harbaum/galagino/images/menu.png

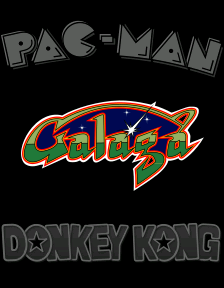
images/menu.png
