harbaum/galagino/galagino/1942_logo.h

const unsigned short _1942_logo[] = {
1,
1, 5841, 0, 41488, 1, 16, 33296, 16648, 1, 29, 0, 1, 21, 33296, 49944, 1, 
4, 1057, 8192, 1, 32, 0, 1, 4, 33296, 8192, 1, 39, 0, 16648, 1, 35, 
33296, 16648, 1, 27, 0, 19555, 57079, 1, 16, 65535, 37524, 1, 27, 0, 16648, 54965, 
1, 27, 65535, 30125, 1, 31, 0, 60250, 1, 26, 65535, 30125, 1, 17, 0, 5021, 
1, 35, 65535, 40431, 59193, 1, 25, 0, 36203, 1, 1, 57079, 1, 14, 23783, 40431, 
65535, 45716, 1, 26, 0, 24840, 63421, 65535, 48887, 1, 20, 23783, 64478, 1, 3, 56022, 
40431, 65535, 45716, 1, 29, 0, 33296, 15591, 65535, 32239, 1, 2, 23783, 32239, 1, 20, 
65535, 30125, 1, 17, 0, 5021, 65535, 40431, 1, 32, 23783, 32239, 65535, 32239, 42545, 1, 
23, 0, 44659, 65535, 57079, 19819, 1, 14, 0, 19555, 65535, 37524, 1, 25, 0, 24840, 
6342, 65535, 64478, 9249, 1, 25, 0, 42545, 40431, 65535, 52851, 1, 28, 0, 53908, 65535, 
63421, 1, 23, 0, 26954, 65535, 30125, 1, 17, 0, 5021, 65535, 52058, 1, 33, 0, 
5021, 65535, 32239, 34353, 1, 21, 0, 61307, 65535, 57079, 60250, 1, 15, 0, 19555, 65535, 
45716, 1, 24, 0, 24840, 14534, 65535, 64478, 1057, 1, 27, 0, 18762, 1, 1, 57079, 
60250, 1, 26, 0, 42545, 57079, 48887, 17441, 1, 23, 0, 26954, 65535, 30125, 1, 17, 
0, 5021, 65535, 52058, 1, 34, 0, 13477, 65535, 15591, 17441, 1, 19, 0, 20876, 65535, 
57079, 52058, 1, 16, 0, 11363, 65535, 45716, 1, 23, 0, 33296, 22726, 65535, 64478, 1057, 
1, 29, 0, 11363, 65535, 48887, 10306, 1, 25, 0, 31182, 65535, 61307, 1, 24, 0, 
35146, 65535, 30125, 1, 17, 0, 5021, 65535, 52058, 1, 34, 0, 8192, 38317, 65535, 7135, 
1057, 1, 17, 0, 29068, 65535, 48887, 35146, 1, 17, 0, 11363, 65535, 45716, 1, 22, 
0, 41488, 31182, 65535, 47830, 49944, 1, 31, 0, 4228, 65535, 40431, 42545, 1, 23, 0, 
36467, 65535, 56022, 8192, 1, 24, 0, 35146, 65535, 21933, 1, 17, 0, 5021, 65535, 52058, 
1, 35, 0, 16648, 63421, 65535, 64478, 58136, 1, 14, 0, 49424, 54445, 65535, 57079, 44429, 
1, 6, 51044, 1, 5, 42852, 41224, 1, 4, 0, 11363, 65535, 45716, 1, 21, 0, 
1074, 64214, 65535, 23519, 2421, 1, 5, 42852, 1, 7, 51044, 1, 8, 59244, 25923, 1, 
9, 0, 62364, 65535, 15591, 9249, 1, 18, 0, 24584, 1, 1, 17202, 58946, 48623, 65535, 
36493, 1, 1, 42852, 34404, 1, 16, 26204, 8473, 1, 4, 0, 35146, 65535, 21933, 1, 
10, 0, 8192, 1, 5, 25394, 62901, 65535, 53149, 1, 25, 51044, 42852, 57616, 1, 8, 
0, 16648, 6078, 65535, 47830, 41488, 1, 12, 0, 41224, 2668, 1, 1, 65535, 28838, 1, 
13, 34933, 57616, 1, 4, 0, 11363, 65535, 45716, 1, 20, 0, 25914, 15327, 65535, 31455, 
51845, 1, 24, 34933, 58426, 1, 8, 0, 8192, 46773, 65535, 47830, 33296, 1, 17, 0, 
9002, 1, 1, 1091, 30398, 65535, 6095, 1, 11, 34933, 51845, 1, 7, 34933, 41505, 1, 
4, 0, 35146, 65535, 21933, 1, 10, 0, 16384, 1, 5, 1091, 13750, 65535, 28838, 1, 
26, 34933, 10093, 57616, 1, 8, 0, 33296, 31182, 65535, 31182, 24840, 1, 10, 0, 49424, 
58426, 1091, 22206, 65535, 14543, 1, 13, 34933, 57616, 1, 4, 0, 11363, 65535, 45716, 1, 
19, 0, 49697, 12437, 65535, 31463, 43645, 1, 26, 34933, 17202, 1, 8, 0, 24840, 22990, 
65535, 13477, 1, 16, 0, 273, 1, 1, 1091, 27764, 65535, 56823, 51845, 1, 11, 34933, 
62918, 43133, 1, 6, 34933, 41505, 1, 4, 0, 35410, 65535, 21669, 1, 10, 0, 16384, 
1, 5, 1091, 13750, 65535, 28838, 1, 27, 34933, 1901, 41224, 1, 8, 0, 41488, 15591, 
65535, 25897, 1, 9, 0, 57616, 58434, 1, 1, 1091, 34643, 40431, 65535, 20382, 1, 12, 
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
