harbaum/galagino/galagino/digdug_logo.h

const unsigned short digdug_logo[] = {
1,
1, 3191, 0, 2114, 13477, 45716, 29068, 4228, 44659, 19819, 2907, 43602, 10306, 59193, 34353, 1057, 
49944, 33296, 1, 189, 0, 24840, 1, 17, 0, 22726, 1, 14, 65535, 40431, 23783, 56022, 
31182, 14534, 54965, 21933, 5021, 45716, 20612, 35146, 1, 8, 0, 30125, 22726, 29068, 43602, 49944, 
1, 98, 0, 17705, 32239, 63421, 29068, 52058, 17705, 1, 54, 0, 9249, 60250, 53908, 39374, 
57079, 62364, 1, 15, 0, 18498, 65535, 63892, 37673, 54065, 5178, 29770, 46418, 62810, 30315, 46963, 
63355, 22660, 39052, 55700, 15013, 39597, 48053, 7102, 31950, 48342, 64990, 32495, 48887, 1, 1, 65535, 
23783, 58136, 1, 7, 0, 34353, 57079, 48887, 1, 2, 65535, 64478, 5021, 19555, 25897, 1, 
94, 0, 53908, 65535, 32495, 1, 2, 65535, 40431, 6078, 29068, 60250, 17705, 1, 44, 0, 
8192, 51001, 44659, 30125, 15591, 1, 2, 65535, 64990, 40142, 65535, 13477, 8192, 1, 13, 0, 
6078, 48887, 62265, 1, 19, 12833, 21025, 7102, 57079, 35146, 1, 8, 0, 30125, 57079, 21570, 
54065, 30315, 63900, 40142, 57079, 1, 1, 65535, 32239, 46773, 53115, 1850, 16648, 1, 88, 0, 
41488, 48887, 15302, 12833, 54065, 13923, 39052, 56245, 24039, 1, 2, 65535, 40431, 6342, 37260, 60250, 
25897, 1, 35, 0, 49944, 35146, 20876, 6342, 48887, 1, 1, 65535, 57079, 40142, 63900, 46963, 
62521, 12833, 21025, 23205, 65535, 30125, 8192, 1, 11, 0, 2114, 65535, 6557, 1, 20, 12833, 
39052, 65535, 29068, 1, 8, 0, 34089, 57079, 39597, 1, 4, 12833, 37673, 46418, 22660, 56245, 
32495, 1, 1, 65535, 57079, 14534, 29068, 35410, 49944, 1, 22, 0, 17441, 52058, 29068, 6078, 
32239, 61307, 1, 55, 0, 61307, 65535, 13923, 1, 5, 12833, 54065, 13923, 39052, 56245, 15847, 
1, 2, 65535, 48887, 14534, 45716, 3171, 34089, 8192, 1, 25, 0, 25897, 19555, 5021, 56022, 
1, 2, 65535, 24039, 56245, 39052, 62810, 29225, 1, 6, 12833, 63900, 65535, 46773, 16648, 1, 
10, 0, 63421, 48887, 62265, 1, 2, 12833, 29481, 40142, 64990, 40142, 23750, 7102, 47797, 31405, 
15013, 55700, 47252, 22660, 63355, 55155, 62810, 1, 1, 12833, 54618, 57079, 22726, 8192, 1, 8, 
0, 30125, 57079, 21570, 1, 8, 12833, 21025, 38218, 6012, 47797, 15847, 1, 2, 65535, 56022, 
5021, 11363, 17705, 1, 13, 0, 17441, 52058, 29068, 63421, 40431, 1, 2, 65535, 24295, 64990, 
65535, 6078, 58136, 1, 52, 0, 8192, 15591, 64990, 21025, 1, 10, 12833, 54065, 13923, 22660, 
31405, 56534, 1, 2, 65535, 48887, 22726, 45716, 11363, 34353, 8192, 1, 15, 0, 24840, 10306, 
61307, 46773, 32239, 1, 2, 65535, 64990, 31405, 55163, 21570, 1, 12, 12833, 22660, 65535, 63421, 
24840, 1, 8, 0, 51001, 65535, 15013, 1, 4, 12833, 38507, 57087, 43755, 42730, 2027, 27115, 
52203, 3564, 28404, 53492, 12789, 39158, 57335, 13923, 12833, 54065, 15847, 32239, 1057, 1, 8, 0, 
25897, 57079, 39597, 1, 5, 12833, 21570, 22115, 45873, 1, 5, 12833, 5178, 46963, 14757, 48342, 
57079, 1, 1, 65535, 32239, 38581, 52851, 49944, 1, 4, 0, 17441, 52058, 29068, 63421, 40431, 
1, 2, 65535, 24295, 64445, 47508, 22115, 62521, 12833, 21025, 55700, 57079, 32239, 43602, 1, 51, 
0, 3171, 65535, 6012, 1, 4, 12833, 21025, 6012, 54610, 37673, 1, 7, 12833, 54065, 13923, 
30860, 56245, 15847, 1, 1, 65535, 40431, 2907, 1, 11, 0, 1057, 52058, 45716, 31182, 57079, 
1, 1, 65535, 40687, 23750, 55700, 13923, 45873, 1, 17, 12833, 6012, 57335, 14534, 33296, 1, 
7, 0, 46773, 57079, 5178, 1, 5, 12833, 7102, 56054, 1002, 1, 5, 58089, 9194, 6903, 
6557, 12833, 21025, 7102, 65535, 43602, 1, 8, 0, 33296, 46773, 57079, 21570, 1, 5, 12833, 
62521, 1, 1, 57335, 56534, 15013, 38763, 5178, 1, 5, 12833, 45873, 13923, 15847, 65535, 48887, 
28011, 0, 17441, 52058, 29068, 63421, 40431, 1, 2, 65535, 24295, 64445, 47508, 22115, 62521, 1, 
7, 12833, 62810, 15847, 65535, 62364, 16648, 1, 49, 0, 39374, 32495, 29481, 1, 5, 12833, 
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
