harbaum/galagino/galagino/frogger_logo.h

const unsigned short frogger_logo[] = {
1,
1, 955, 0, 8208, 33320, 58192, 1129, 18049, 1, 3, 17777, 1121, 41792, 16672, 1, 206, 
0, 41792, 26241, 51369, 10690, 1, 13, 19154, 10698, 59569, 34441, 41792, 1, 197, 0, 25128, 
26249, 2234, 1, 23, 19154, 2490, 9585, 8200, 1, 190, 0, 24864, 34441, 10698, 1, 29, 
19154, 2234, 58456, 1, 186, 0, 1121, 2498, 1, 34, 19154, 18898, 1113, 1, 181, 0, 
8, 26249, 10706, 1, 14, 19154, 10706, 2498, 51369, 1, 3, 42905, 42913, 59569, 10698, 1, 
13, 19154, 10690, 8208, 1, 178, 0, 26241, 18898, 1, 11, 19154, 59569, 18049, 58456, 33328, 
8208, 1, 9, 0, 8, 25128, 50000, 17785, 59569, 1, 10, 19154, 41528, 1, 175, 0, 
9577, 10706, 1, 9, 19154, 2498, 18049, 49992, 8208, 1, 2, 0, 16392, 16417, 8514, 57682, 
24931, 57971, 1, 1, 628, 57971, 33387, 8539, 24906, 32809, 32784, 1, 2, 0, 8208, 50000, 
42905, 1, 8, 19154, 49976, 1, 172, 0, 24872, 2242, 1, 8, 19154, 10698, 26241, 33336, 
1, 2, 0, 33, 33098, 636, 33701, 1, 13, 41926, 58293, 41612, 49490, 25, 1, 1, 
0, 8208, 9577, 10698, 1, 6, 19154, 25112, 1, 170, 0, 34449, 1, 8, 19154, 59569, 
58456, 8, 1, 1, 0, 41009, 57971, 950, 1, 21, 41926, 33701, 8547, 49176, 0, 8, 
9585, 1, 5, 19154, 27322, 1, 168, 0, 24872, 10698, 1, 7, 19154, 51369, 41528, 1, 
1, 0, 8225, 41579, 58293, 1, 26, 41926, 33734, 25220, 49176, 0, 41528, 10698, 1, 4, 
19154, 59225, 1, 166, 0, 1121, 1, 7, 19154, 59569, 41792, 1, 1, 0, 41009, 49804, 
1, 31, 41926, 25534, 16706, 0, 41792, 1, 4, 19154, 27330, 8192, 1, 164, 0, 42913, 
1, 6, 19154, 10698, 58456, 1, 1, 0, 314, 9117, 1, 34, 41926, 33734, 314, 0, 
26241, 1, 4, 19154, 59185, 1, 162, 0, 8208, 2498, 1, 6, 19154, 34713, 16664, 0, 
25, 58004, 1, 37, 41926, 9150, 24584, 8464, 18898, 1, 3, 19154, 35458, 1, 161, 0, 
16672, 10698, 1, 5, 19154, 10698, 49992, 0, 8192, 25195, 33734, 1, 39, 41926, 347, 0, 
42913, 1, 3, 19154, 35498, 16640, 1, 159, 0, 24864, 10706, 1, 5, 19154, 51369, 16664, 
0, 49457, 50093, 1, 41, 41926, 58004, 0, 9585, 1, 3, 19154, 27322, 9241, 1, 158, 
0, 33320, 10706, 1, 5, 19154, 26241, 1, 1, 0, 16739, 33734, 1, 42, 41926, 50093, 
0, 58456, 1, 3, 19154, 27330, 34345, 1, 157, 0, 33328, 18898, 1, 5, 19154, 1113, 
0, 40976, 17309, 1, 44, 41926, 58293, 0, 58456, 1, 3, 19154, 27338, 59185, 1, 156, 
0, 8208, 10706, 1, 4, 19154, 10706, 41792, 0, 32809, 950, 1, 45, 41926, 17309, 0, 
9577, 1, 3, 19154, 27322, 59185, 1, 156, 0, 2498, 1, 4, 19154, 10698, 41528, 0, 
314, 25542, 1, 46, 41926, 41579, 0, 34449, 1, 3, 19154, 35506, 42537, 1, 155, 0, 
51369, 1, 4, 19154, 10698, 33336, 0, 49490, 33734, 1, 47, 41926, 49457, 0, 2498, 1, 
3, 19154, 43922, 17697, 1, 154, 0, 26241, 1, 4, 19154, 18898, 33328, 0, 49490, 1, 
48, 41926, 950, 8192, 33328, 1, 4, 19154, 60258, 16640, 1, 153, 0, 33328, 1, 5, 
19154, 58456, 0, 33098, 1, 49, 41926, 8539, 0, 26249, 1, 4, 19154, 60234, 1, 154, 
0, 10698, 1, 4, 19154, 17777, 0, 49457, 33734, 1, 48, 41926, 9142, 24584, 8464, 10706, 
1, 3, 19154, 35498, 18490, 1, 38, 0, 8208, 1, 7, 0, 49992, 17785, 1, 1, 
34705, 1129, 8208, 1, 99, 0, 18049, 1, 4, 19154, 42913, 0, 33, 9142, 1, 49, 
41926, 41290, 0, 26241, 1, 4, 19154, 60258, 49936, 1, 33, 0, 25128, 34441, 2498, 10706, 
1, 3, 19154, 10706, 59569, 17785, 25128, 42905, 18898, 1, 5, 19154, 10690, 1121, 1, 96, 
0, 8200, 1, 4, 19154, 10698, 16664, 8192, 25509, 1, 49, 41926, 49804, 0, 25128, 1, 
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
