harbaum/galagino/galagino/dkong_logo.h

const unsigned short dkong_logo[] = {
1,
1, 6912, 0, 8192, 32784, 49184, 1, 33, 0, 24592, 1, 1, 57376, 1, 1, 16689, 
1, 1, 49473, 24881, 32784, 1, 19, 0, 8200, 24592, 1, 22, 0, 40984, 586, 33370, 
58218, 17275, 42123, 1172, 25764, 8778, 0, 8192, 25178, 883, 41826, 8778, 24881, 32784, 1, 21, 
0, 24584, 40984, 289, 24881, 49473, 16978, 33370, 41826, 16681, 1, 54, 0, 24592, 1, 13, 
0, 24592, 57376, 24881, 57665, 25178, 58218, 25178, 16392, 1, 1, 0, 883, 17861, 42453, 1758, 
26350, 1, 2, 42742, 17861, 24840, 1, 1, 0, 24592, 25178, 33667, 1172, 42115, 17275, 58218, 
33370, 8786, 49729, 16689, 57376, 24592, 1, 12, 0, 57376, 17572, 1758, 1, 9, 42742, 59101, 
1172, 41529, 1, 12, 0, 49176, 9075, 1469, 18158, 1, 2, 42742, 59101, 50604, 58218, 41240, 
1, 2, 0, 32784, 586, 33378, 883, 33667, 58515, 25764, 58804, 17861, 50645, 18150, 42709, 57929, 
8192, 8489, 26350, 1, 6, 42742, 34550, 545, 9083, 1, 6, 42742, 18158, 17564, 33040, 1, 
3, 0, 297, 16689, 289, 8786, 25467, 1172, 17564, 33964, 58804, 17861, 42453, 1758, 18158, 1, 
9, 42742, 9917, 50901, 26350, 42742, 50901, 57921, 1, 4, 0, 16392, 883, 33667, 17275, 50026, 
8786, 41529, 32792, 1, 7, 0, 24592, 1, 1, 57376, 8489, 1, 1, 16689, 16392, 1, 
4, 0, 57665, 58218, 17275, 1, 1, 42115, 58507, 58515, 883, 33040, 1, 1, 0, 24584, 
41570, 42156, 1758, 1, 2, 42742, 9958, 1469, 17275, 297, 1, 3, 0, 41570, 17861, 50645, 
18150, 1, 7, 42742, 34212, 16648, 49473, 42742, 18158, 34517, 18125, 1725, 42676, 34476, 34509, 42742, 
25690, 33040, 41867, 26350, 1, 11, 42742, 9958, 58804, 50018, 24592, 1, 7, 0, 8192, 50645, 
1, 1, 42742, 26358, 1758, 59101, 34517, 34509, 1, 1, 9925, 1725, 34517, 9958, 1, 2, 
42742, 1469, 289, 1, 8, 0, 40984, 9372, 34550, 1, 1, 42742, 34550, 1758, 50901, 1766, 
34550, 1, 1, 42742, 34550, 9372, 57632, 24584, 59101, 1, 4, 42742, 26350, 1766, 50901, 26317, 
18117, 34550, 1766, 41488, 58218, 42742, 1444, 58754, 25978, 58737, 25961, 17769, 50587, 42742, 9290, 1436, 
18158, 58754, 50562, 9611, 34195, 58779, 34476, 26317, 42742, 9620, 16648, 1, 1, 0, 1469, 1, 
3, 42742, 1, 1, 34550, 18158, 1758, 34509, 18125, 18117, 1733, 50876, 34228, 26284, 1444, 50587, 
34195, 34203, 26259, 9611, 58762, 34550, 1725, 42635, 9644, 34484, 9958, 18158, 41496, 1, 3, 0, 
58515, 1, 6, 42742, 50901, 33337, 1, 2, 0, 41273, 59101, 1, 6, 42742, 26350, 8786, 
8192, 1, 1, 0, 33964, 1, 7, 42742, 17861, 33040, 17275, 18158, 1, 1, 42742, 34550, 
1766, 50909, 1766, 34550, 1, 2, 42742, 50612, 24881, 0, 49176, 34550, 26350, 34509, 9925, 50868, 
26284, 1436, 42387, 9611, 58754, 42362, 1725, 42742, 58433, 41826, 42742, 58754, 9569, 1137, 1145, 1, 
1, 58496, 25738, 42742, 17779, 26276, 18158, 1733, 50570, 42345, 17769, 25961, 50545, 9594, 34178, 58754, 
17803, 42387, 1444, 34476, 18117, 18158, 42742, 9958, 57921, 8192, 1, 5, 0, 49473, 42742, 42709, 
58721, 17753, 9569, 17769, 9321, 1, 2, 1137, 1, 1, 58488, 1137, 58737, 42387, 1766, 42742, 
26350, 41826, 8192, 1, 5, 0, 25178, 18158, 42742, 18158, 17828, 34162, 25945, 9569, 17769, 9321, 
34153, 58754, 50868, 34550, 42742, 18158, 17531, 9958, 9644, 17778, 58737, 34153, 9577, 17769, 9321, 1, 
1, 1137, 1145, 34203, 42742, 9587, 58218, 42742, 25970, 58496, 41896, 33720, 25280, 25288, 42154, 42742, 
34138, 1436, 26317, 9561, 50072, 33704, 41888, 41880, 50064, 58504, 1766, 1725, 41496, 8192, 41570, 42742, 
1477, 50587, 9892, 50876, 59068, 9925, 59101, 42742, 1733, 9569, 1137, 1145, 1, 1, 58496, 58504, 
1, 1, 50320, 1, 1, 41880, 41888, 41896, 33712, 59109, 18117, 17753, 1145, 58504, 26011, 42742, 
42082, 16648, 1, 1, 0, 24584, 26350, 18125, 1386, 9586, 34170, 50562, 9611, 1444, 34550, 42412, 
24840, 1, 1, 0, 41867, 42742, 18117, 26028, 1444, 50587, 34195, 1, 1, 26003, 1758, 59101, 
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
