harbaum/galagino/galagino/galaga_logo.h

const unsigned short galaga_logo[] = {
1,
1, 1006, 0, 33296, 1057, 34353, 2114, 26954, 60250, 19819, 52851, 12420, 1, 3, 44659, 11363, 
60250, 18762, 50737, 9249, 33296, 1, 196, 0, 24840, 34089, 35146, 36203, 37260, 38317, 39374, 40431, 
1, 18, 65535, 57079, 64478, 63421, 62364, 61307, 2907, 59193, 33296, 1, 16, 0, 2114, 33296, 
1, 164, 0, 58136, 26954, 61307, 30125, 64478, 1, 3, 65535, 32255, 47870, 63485, 13565, 29180, 
4092, 44795, 11515, 1, 1, 43770, 10490, 1, 3, 2298, 18938, 1, 1, 43770, 3323, 36603, 
12540, 45820, 21757, 63485, 64510, 48895, 1, 4, 65535, 23783, 63421, 45716, 11363, 42545, 8192, 1, 
8, 0, 33296, 62364, 31182, 1, 160, 0, 33296, 26954, 20876, 55229, 23783, 1, 1, 65535, 
40447, 22782, 54012, 36347, 35322, 26105, 25080, 1, 1, 248, 8440, 41208, 8441, 33017, 49401, 8442, 
24826, 33018, 49402, 1, 3, 57594, 41210, 33018, 24826, 8442, 49401, 24825, 249, 41208, 8440, 1, 
1, 248, 50168, 42745, 43770, 4092, 21757, 39422, 48895, 1, 2, 65535, 48887, 22726, 45716, 3171, 
34089, 8192, 1, 2, 0, 43602, 15591, 65535, 12420, 1, 156, 0, 41488, 35146, 29068, 31182, 
57079, 65535, 7167, 38397, 12540, 43770, 17657, 1, 1, 248, 57592, 49401, 33018, 16635, 41187, 41155, 
32939, 16531, 49266, 16730, 57673, 1, 1, 57665, 57921, 1, 2, 49729, 8778, 49721, 57921, 49729, 
57921, 49473, 57665, 49473, 330, 24930, 49266, 16531, 32947, 41163, 33003, 251, 24826, 33017, 41208, 1, 
1, 248, 26105, 3323, 45820, 22782, 48895, 1, 2, 65535, 40431, 54965, 53115, 38317, 65535, 64478, 
65535, 2114, 1, 152, 0, 8192, 2114, 29068, 39374, 57079, 65535, 47870, 45820, 52218, 58360, 248, 
16632, 24825, 24826, 16627, 41171, 32931, 41322, 57673, 57921, 49721, 17218, 1363, 34651, 2412, 35452, 2949, 
27789, 1, 13, 35989, 19341, 60292, 35444, 2412, 26459, 50514, 9026, 57913, 49473, 338, 57466, 32939, 
41171, 16627, 8442, 57592, 248, 8440, 59385, 61435, 6142, 48895, 1, 2, 65535, 30125, 48887, 57079, 
58136, 1, 149, 0, 33296, 52058, 21669, 32239, 65535, 7167, 45820, 35578, 41720, 248, 49400, 8442, 
24819, 41147, 8331, 8530, 49473, 57913, 42058, 43107, 43644, 27789, 1, 1, 35989, 19341, 35444, 59499, 
26459, 58706, 25674, 57913, 1, 1, 57921, 49729, 57921, 57665, 1, 3, 49473, 586, 49729, 57921, 
57913, 9026, 33866, 58706, 34651, 18796, 60028, 27789, 1, 2, 35989, 19341, 26996, 34651, 33866, 57913, 
49473, 33130, 32939, 41179, 49402, 24825, 8440, 16888, 18682, 29180, 52875, 56022, 1, 2, 65535, 47830, 
20612, 42545, 1, 28, 0, 9249, 18762, 1, 2, 43602, 26954, 42545, 16648, 1, 106, 0, 
58136, 36467, 6078, 57079, 57087, 14590, 53243, 34297, 248, 49400, 16634, 33011, 49339, 41074, 49473, 57921, 
1619, 10604, 11149, 1, 1, 35989, 19341, 10604, 18011, 25674, 49721, 49473, 338, 49266, 24723, 24755, 
41163, 41187, 33011, 8443, 57594, 1, 1, 33018, 24826, 1, 1, 8442, 16634, 1, 1, 33018, 
41210, 57594, 24827, 33003, 41179, 41155, 32939, 131, 33130, 57673, 49473, 57913, 33866, 18267, 18804, 19341, 
1, 2, 35989, 51836, 34651, 25674, 49721, 8538, 24739, 41187, 33018, 32896, 176, 34297, 61435, 31230, 
1, 3, 65535, 39374, 28011, 33296, 1, 21, 0, 16648, 52058, 13477, 23783, 1, 1, 65535, 
23807, 56062, 15615, 1, 1, 65535, 57079, 38581, 25897, 1, 101, 0, 24840, 2907, 63421, 57079, 
57087, 63485, 19707, 41720, 248, 24825, 243, 49347, 41074, 49473, 57921, 9819, 35444, 27789, 1, 1, 
35989, 43644, 26459, 17218, 49721, 330, 131, 41139, 32987, 57594, 16634, 33017, 49400, 1, 2, 248, 
232, 464, 704, 696, 688, 1, 6, 928, 688, 704, 456, 17112, 240, 1, 1, 248, 
16632, 57592, 41209, 24826, 16635, 41179, 41139, 131, 338, 49729, 9026, 9819, 26996, 27789, 1, 1, 
35989, 2949, 42851, 9026, 8745, 24881, 49347, 243, 16633, 248, 1273, 61435, 56062, 1, 2, 65535, 
48887, 13477, 59193, 1, 16, 0, 8192, 26954, 13477, 40431, 56062, 37372, 51962, 9465, 8440, 1, 
2, 248, 25080, 10490, 55037, 65535, 48887, 25897, 1, 97, 0, 8192, 26954, 13477, 40431, 65535, 
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
