harbaum/galagino/galagino/pacman_logo.h

const unsigned short pacman_logo[] = {
1,
1, 4555, 0, 41480, 1041, 17689, 58128, 16640, 1, 214, 0, 49936, 3139, 45924, 63869, 1, 
1, 23174, 55421, 1, 1, 30325, 13677, 12628, 10538, 16640, 1, 208, 0, 26137, 37732, 1, 
1, 14982, 45924, 52282, 17689, 16640, 1, 3, 0, 8192, 17689, 27186, 35378, 33288, 1, 204, 
0, 24840, 4436, 23174, 63869, 28235, 49936, 0, 57376, 33378, 41867, 25780, 1, 1, 58556, 25780, 
50067, 33378, 8489, 0, 24840, 17689, 1, 35, 0, 8224, 16, 1, 164, 0, 17689, 38773, 
23174, 4436, 33288, 8200, 41578, 9421, 1, 9, 9718, 25813, 635, 24592, 1, 1, 8192, 1, 
28, 0, 17689, 18738, 1, 2, 0, 16712, 33432, 1, 163, 0, 34337, 1, 1, 63869, 
2090, 0, 25178, 42461, 1, 13, 9718, 58861, 57970, 8192, 1, 28, 0, 59433, 6534, 8192, 
33378, 16392, 8232, 50136, 16720, 1, 161, 0, 17689, 63869, 46965, 9241, 32784, 33972, 1, 17, 
9718, 9421, 57376, 1, 27, 0, 35634, 23174, 25096, 924, 50067, 0, 33432, 50128, 24, 1, 
159, 0, 24840, 30581, 47229, 58128, 57376, 25813, 1, 19, 9718, 58853, 41281, 1, 26, 0, 
11587, 14982, 0, 42164, 9718, 338, 16, 41920, 41640, 1, 20, 0, 41480, 1, 115, 0, 
11587, 24840, 1, 2, 0, 8232, 1, 15, 0, 4436, 6534, 17689, 49184, 34269, 1, 21, 
9718, 1518, 41281, 1, 25, 0, 61523, 38773, 0, 17613, 9718, 50661, 40984, 8504, 50136, 16736, 
1, 18, 0, 42785, 4436, 1, 2, 0, 8, 24, 1, 109, 0, 8192, 55421, 52026, 
1, 1, 0, 32, 41920, 8, 1, 13, 0, 34337, 23174, 43826, 16392, 17613, 1, 23, 
9718, 58861, 57376, 1, 24, 0, 45924, 62572, 0, 50661, 1, 1, 9718, 42172, 0, 25208, 
50128, 8224, 1, 16, 0, 35378, 13933, 33288, 32784, 25475, 0, 33432, 8232, 1, 109, 0, 
50977, 23174, 50977, 49473, 25483, 0, 33440, 33432, 1, 13, 0, 37732, 54372, 0, 58267, 1, 
25, 9718, 42172, 1, 24, 0, 22125, 20828, 8200, 1, 3, 9718, 49778, 0, 1, 1, 
41904, 1, 15, 0, 44875, 5485, 33288, 49184, 17621, 924, 0, 50136, 16, 1, 16, 0, 
1041, 1, 64, 0, 8192, 26137, 52026, 53331, 62564, 22133, 29276, 44875, 43834, 2090, 26137, 24840, 
1, 14, 0, 61523, 55421, 0, 58267, 9718, 57673, 16, 41920, 16736, 1, 11, 0, 58128, 
14982, 17689, 41281, 1, 25, 9718, 17316, 32792, 1, 24, 0, 63869, 44875, 57376, 1, 3, 
9718, 1526, 16689, 8224, 50128, 25200, 1, 12, 0, 16640, 29276, 45924, 16640, 41, 34269, 9718, 
17283, 16, 50136, 1, 16, 0, 1041, 55421, 24840, 1, 2, 0, 8232, 1, 55, 0, 
41480, 2090, 28235, 62564, 6526, 13677, 53067, 18738, 1041, 1, 1, 0, 8192, 41, 1, 1, 
8497, 49184, 1, 13, 0, 8192, 63869, 53331, 8192, 50661, 9718, 50661, 49184, 8240, 50128, 8232, 
1, 10, 0, 3395, 37468, 0, 58564, 1, 23, 9718, 42461, 338, 0, 8240, 1, 23, 
0, 16640, 23174, 60474, 24889, 1, 4, 9718, 17621, 16392, 16736, 50136, 8240, 1, 10, 0, 
49936, 22125, 21084, 8192, 33081, 50661, 1, 1, 9718, 49770, 8232, 41920, 1, 15, 0, 25096, 
22133, 30581, 8192, 49473, 49481, 8, 50120, 8, 1, 50, 0, 17689, 43834, 4436, 38773, 63613, 
37732, 3395, 50977, 24840, 0, 8192, 24889, 49778, 17316, 17621, 1, 4, 9718, 58861, 50364, 25186, 
16392, 8, 16, 1, 7, 0, 59433, 23174, 42529, 57673, 1, 2, 9718, 1221, 8192, 24936, 
41920, 8, 1, 9, 0, 54372, 59433, 24889, 1, 23, 9718, 58267, 24592, 16, 33424, 50136, 
16720, 1, 22, 0, 1041, 23174, 18738, 338, 1, 5, 9718, 41875, 0, 33432, 41920, 8, 
1, 8, 0, 26137, 47229, 61523, 0, 57673, 1518, 1, 2, 9718, 8530, 8512, 41640, 1, 
14, 0, 8192, 62564, 63869, 1041, 41, 50661, 41867, 8, 50128, 8504, 1, 45, 0, 16640, 
42785, 11587, 37732, 63869, 13677, 44875, 18738, 58128, 1, 1, 0, 40984, 338, 25483, 58564, 1526, 
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
