harbaum/galagino/galagino/galaga_starseed.h

struct galaga_star { unsigned char x, y; unsigned short col; };
const struct galaga_star galaga_star_set[][63] = {
 {
  { 0x85, 0x06, 0xbf52 },
  { 0x8f, 0x08, 0x1f00 },
  { 0xe5, 0x1b, 0xa0fa },
  { 0x22, 0x1c, 0x1f50 },
  { 0xe5, 0x25, 0xea57 },
  { 0x15, 0x26, 0x5455 },
  { 0x80, 0x2d, 0x5ffd },
  { 0x97, 0x2e, 0xea07 },
  { 0xba, 0x3b, 0xa052 },
  { 0x36, 0x3d, 0xbfa2 },
  { 0x57, 0x44, 0x4055 },
  { 0xcf, 0x44, 0xff57 },
  { 0x61, 0x4e, 0xb4fa },
  { 0x87, 0x64, 0x4aa5 },
  { 0xd6, 0x64, 0xaafa },
  { 0x0b, 0x6c, 0xff07 },
  { 0x06, 0x6d, 0xb402 },
  { 0x18, 0x6e, 0x5fa5 },
  { 0xa9, 0x79, 0x14f8 },
  { 0x8a, 0x7b, 0x0a50 },
  { 0xd6, 0x80, 0xe007 },
  { 0x67, 0x82, 0xffff },
  { 0x39, 0x83, 0x5f05 },
  { 0x72, 0x83, 0xaa02 },
  { 0xec, 0x84, 0xaaa2 },
  { 0x8e, 0x85, 0x0a00 },
  { 0x20, 0x88, 0xb452 },
  { 0x95, 0x8a, 0xe0ff },
  { 0x0e, 0x8d, 0x0000 },
  { 0x06, 0x91, 0xf4a7 },
  { 0x07, 0x94, 0xe057 },
  { 0xae, 0x97, 0x40fd },
  { 0x00, 0x98, 0xf457 },
  { 0x86, 0x9b, 0x0050 },
  { 0x58, 0xa1, 0xbf02 },
  { 0xfe, 0xa1, 0xffa7 },
  { 0xa2, 0xa8, 0xeaff },
  { 0x41, 0xaa, 0x40a5 },
  { 0x3f, 0xac, 0x1fa0 },
  { 0xde, 0xac, 0x00f8 },
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
 },
 {
  { 0xfe, 0x04, 0xff57 },
  { 0xc4, 0x06, 0x0a00 },
  { 0x1e, 0x07, 0xf457 },
  { 0x83, 0x0b, 0xeaff },
  { 0x2e, 0x0d, 0xff07 },
  { 0x1f, 0x0e, 0x0000 },
  { 0xd8, 0x0e, 0xf407 },
  { 0x03, 0x0f, 0xaafa },
  { 0x95, 0x11, 0xffff },
  { 0x6a, 0x17, 0xbf52 },
  { 0xcc, 0x17, 0x00a0 },
  { 0x00, 0x18, 0x1fa0 },
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
  { 0x35, 0x69, 0x1400 },
  { 0x8f, 0x6c, 0xa002 },
  { 0xca, 0x6c, 0x54a5 },
  { 0x5a, 0x74, 0x4055 },
  { 0x60, 0x78, 0x5f05 },
  { 0x72, 0x79, 0xeaa7 },
  { 0x37, 0x7f, 0x5455 },
  { 0x12, 0x80, 0xaa02 },
  { 0x29, 0x82, 0x54fd },
  { 0x84, 0x98, 0xbfa2 },
  { 0x32, 0x99, 0xbffa },
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
 }
};
