harbaum/galagino/galagino/tileaddr.h

const unsigned short tileaddr[][28] = {
 {989, 988, 987, 986, 985, 984, 983, 982, 981, 980, 979, 978, 977, 976, 975, 974, 973, 972, 971, 970, 969, 968, 967, 966, 965, 964, 963, 962},
 {1021, 1020, 1019, 1018, 1017, 1016, 1015, 1014, 1013, 1012, 1011, 1010, 1009, 1008, 1007, 1006, 1005, 1004, 1003, 1002, 1001, 1000, 999, 998, 997, 996, 995, 994},
 {928, 896, 864, 832, 800, 768, 736, 704, 672, 640, 608, 576, 544, 512, 480, 448, 416, 384, 352, 320, 288, 256, 224, 192, 160, 128, 96, 64},
 {929, 897, 865, 833, 801, 769, 737, 705, 673, 641, 609, 577, 545, 513, 481, 449, 417, 385, 353, 321, 289, 257, 225, 193, 161, 129, 97, 65},
 {930, 898, 866, 834, 802, 770, 738, 706, 674, 642, 610, 578, 546, 514, 482, 450, 418, 386, 354, 322, 290, 258, 226, 194, 162, 130, 98, 66},
 {931, 899, 867, 835, 803, 771, 739, 707, 675, 643, 611, 579, 547, 515, 483, 451, 419, 387, 355, 323, 291, 259, 227, 195, 163, 131, 99, 67},
 {932, 900, 868, 836, 804, 772, 740, 708, 676, 644, 612, 580, 548, 516, 484, 452, 420, 388, 356, 324, 292, 260, 228, 196, 164, 132, 100, 68},
 {933, 901, 869, 837, 805, 773, 741, 709, 677, 645, 613, 581, 549, 517, 485, 453, 421, 389, 357, 325, 293, 261, 229, 197, 165, 133, 101, 69},
 {934, 902, 870, 838, 806, 774, 742, 710, 678, 646, 614, 582, 550, 518, 486, 454, 422, 390, 358, 326, 294, 262, 230, 198, 166, 134, 102, 70},
 {935, 903, 871, 839, 807, 775, 743, 711, 679, 647, 615, 583, 551, 519, 487, 455, 423, 391, 359, 327, 295, 263, 231, 199, 167, 135, 103, 71},
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
 {29, 28, 27, 26, 25, 24, 23, 22, 21, 20, 19, 18, 17, 16, 15, 14, 13, 12, 11, 10, 9, 8, 7, 6, 5, 4, 3, 2},
 {61, 60, 59, 58, 57, 56, 55, 54, 53, 52, 51, 50, 49, 48, 47, 46, 45, 44, 43, 42, 41, 40, 39, 38, 37, 36, 35, 34}
};
