harbaum/galagino/galagino/dkong_sample_jump.h

const unsigned char dkong_sample_jump[] = {
  0x00,0x00,0x00,0xFF,0xFF,0x00,0xFF,0xFF,0xFE,0x00,0xFF,0x00,0x00,0x01,0xFF,0x00,
  0x00,0xFE,0x00,0x00,0x00,0xFF,0xFF,0xFF,0x00,0xFE,0x00,0x00,0xFF,0x00,0x00,0xFF,
  0xFF,0xFF,0x00,0x00,0xFF,0x00,0xFF,0x01,0xFF,0x00,0x00,0xFF,0x00,0xFF,0x01,0xFF,
  0x00,0x00,0x00,0x01,0x00,0xFF,0x01,0xFF,0xFF,0xFF,0xFF,0xFF,0x00,0x00,0x00,0x00,
  0x00,0xFE,0xFF,0xFE,0x01,0xFF,0x01,0xFF,0x03,0xF9,0xA9,0x81,0x81,0x82,0x8B,0x90,
  0x97,0x9E,0xA5,0xAA,0xAF,0xB4,0xBA,0xBE,0xC2,0xC6,0xCC,0xCB,0xD4,0xD0,0xF9,0x4C,
  0x61,0x63,0x60,0x5A,0x56,0x50,0x4B,0x47,0x42,0x40,0x3C,0x39,0x37,0x30,0x34,0x00,
  0xB3,0xA7,0xA4,0xAA,0xAF,0xB2,0xB8,0xBB,0xC0,0xC6,0xC7,0xCC,0xD1,0xD3,0xDA,0xD9,
  0x18,0x5D,0x67,0x66,0x60,0x5C,0x55,0x50,0x4D,0x47,0x46,0x45,0x3E,0x3A,0x36,0x34,
  0x2E,0xE6,0xAC,0xA5,0xA7,0xAD,0xB0,0xB7,0xB9,0xBB,0xC3,0xC5,0xC7,0xCD,0xCF,0xD5,
  0xD5,0xE1,0x31,0x61,0x66,0x63,0x5D,0x5D,0x53,0x53,0x4D,0x47,0x43,0x41,0x3A,0x3B,
  0x34,0x38,0x22,0xD0,0xA7,0xA3,0xA6,0xAB,0xAE,0xB6,0xB7,0xBC,0xC3,0xC6,0xCD,0xD0,
  0xD0,0xD7,0xD2,0xF5,0x45,0x63,0x67,0x61,0x5E,0x59,0x51,0x51,0x48,0x47,0x43,0x3D,
  0x3A,0x38,0x34,0x38,0x0B,0xC0,0xA9,0xA4,0xA9,0xAA,0xAE,0xB6,0xB9,0xC3,0xC5,0xC7,
  0xCC,0xCF,0xD1,0xD2,0xCF,0x07,0x4F,0x60,0x64,0x5F,0x60,0x5B,0x55,0x4E,0x43,0x42,
  0x40,0x3C,0x37,0x36,0x36,0x35,0xF4,0xB2,0xA5,0xA2,0xA5,0xA3,0xA7,0xAD,0xB7,0xC4,
  0xC4,0xC3,0xCA,0xCF,0xD2,0xD1,0xD9,0x21,0x59,0x61,0x60,0x5D,0x62,0x5E,0x59,0x4E,
  0x42,0x44,0x44,0x3B,0x36,0x31,0x31,0x23,0xD5,0xA7,0xA2,0xA3,0xA7,0xA9,0xB2,0xB6,
  0xC2,0xC8,0xC4,0xC7,0xD2,0xD4,0xDB,0xD8,0xED,0x3F,0x62,0x64,0x64,0x60,0x5A,0x50,
  0x4D,0x42,0x40,0x40,0x3C,0x33,0x30,0x2B,0x30,0x10,0xBC,0xA5,0xA4,0xA1,0xA4,0xAD,
  0xB5,0xB7,0xC2,0xC4,0xC7,0xCC,0xD3,0xD4,0xD8,0xD0,0xFC,0x4E,0x5D,0x62,0x64,0x62,
  0x56,0x4E,0x4B,0x41,0x40,0x3C,0x37,0x32,0x31,0x2F,0x36,0xFC,0xB3,0xA8,0xA2,0xA0,
  0xA3,0xB1,0xB9,0xBE,0xC3,0xC3,0xC6,0xCA,0xCF,0xD1,0xD1,0xCE,0x12,0x54,0x5D,0x63,
  0x5F,0x5B,0x4D,0x46,0x41,0x40,0x3F,0x3A,0x36,0x32,0x2E,0x32,0x2E,0xE5,0xAA,0xA0,
  0x9D,0xA5,0xAC,0xB7,0xBE,0xC2,0xBF,0xC4,0xC8,0xCD,0xCF,0xD3,0xCF,0xD9,0x29,0x5A,
  0x61,0x63,0x59,0x54,0x49,0x43,0x41,0x43,0x3D,0x38,0x32,0x31,0x2D,0x34,0x20,0xCF,
  0xA7,0xA1,0xA4,0xA8,0xAE,0xB9,0xBE,0xBF,0xBF,0xC7,0xC9,0xD0,0xCF,0xD3,0xCA,0xE7,
  0x39,0x58,0x5C,0x59,0x58,0x52,0x47,0x40,0x3F,0x40,0x39,0x37,0x32,0x32,0x30,0x3C,
  0x11,0xC0,0xA9,0xA7,0xAB,0xA8,0xB1,0xBC,0xC2,0xBF,0xC0,0xC7,0xCA,0xCE,0xCD,0xCD,
  0xC2,0xFB,0x4A,0x5A,0x58,0x54,0x54,0x4C,0x43,0x3F,0x41,0x3B,0x35,0x32,0x31,0x30,
  0x32,0x37,0xEF,0xA7,0xA3,0xAA,0xAB,0xAB,0xB4,0xB7,0xBF,0xC0,0xC6,0xCA,0xCF,0xCD,
  0xCF,0xCF,0xD3,0x25,0x5B,0x58,0x5C,0x56,0x53,0x4E,0x49,0x41,0x3F,0x39,0x35,0x32,
  0x35,0x30,0x32,0x23,0xD2,0xA1,0x9C,0xA2,0xA8,0xAA,0xB3,0xBA,0xBD,0xC0,0xC6,0xC9,
  0xCB,0xC9,0xD1,0xD1,0xEA,0x3B,0x5E,0x5F,0x5B,0x58,0x53,0x4A,0x46,0x41,0x3E,0x3A,
  0x38,0x36,0x34,0x2B,0x2D,0x09,0xBD,0xA4,0xA0,0xA4,0xA9,0xAD,0xB4,0xB7,0xBC,0xBF,
  0xC2,0xC8,0xCC,0xCE,0xD6,0xD4,0x01,0x49,0x5C,0x5E,0x5A,0x58,0x53,0x4B,0x45,0x40,
  0x3D,0x38,0x34,0x2D,0x2C,0x27,0x29,0xF5,0xAF,0xA0,0xA1,0xA6,0xAA,0xB0,0xB4,0xBA,
  0xC1,0xC4,0xC6,0xCD,0xD0,0xD2,0xD4,0xD6,0x18,0x56,0x5D,0x5F,0x58,0x52,0x4D,0x48,
  0x41,0x3D,0x37,0x37,0x33,0x2F,0x2B,0x2A,0x21,0xDA,0xA6,0xA3,0xA1,0xA9,0xAF,0xB3,
  0xB8,0xBE,0xC3,0xC6,0xC4,0xCC,0xCE,0xD2,0xD2,0xE3,0x30,0x5A,0x5B,0x5A,0x54,0x4F,
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
};
