harbaum/galagino/galagino/dkong_sample_stomp.h

const unsigned char dkong_sample_stomp[] = {
  0xFE,0xFE,0xFE,0xFE,0xFE,0xFF,0xFF,0xFE,0xFE,0xFE,0xFE,0xFE,0xFE,0xFE,0xFD,0xFE,
  0xFE,0xFF,0xFF,0xFD,0xFE,0xFE,0xFF,0xFE,0xFE,0xFE,0xFE,0xFE,0xFE,0xFE,0xFE,0xFF,
  0xFE,0xFE,0xFF,0xFE,0xFE,0xFE,0x00,0xFE,0x00,0xFF,0xFE,0xFD,0x00,0x00,0xFF,0x01,
  0xFF,0x00,0x01,0x00,0x00,0x00,0xFF,0x01,0x01,0x00,0x00,0x01,0x00,0x00,0x00,0xFE,
  0x01,0xFF,0xFF,0xFF,0x00,0x00,0x00,0xFF,0x00,0x00,0x00,0xFE,0xFF,0xFE,0xFE,0xFF,
  0xFF,0xFE,0xFE,0xFE,0xFE,0xFF,0xFE,0xFF,0xFE,0xFE,0xFE,0xFE,0xFF,0xFE,0xFE,0xFE,
  0xFF,0xFE,0xFE,0xFE,0xFE,0xFE,0xFE,0xFE,0xFF,0xFE,0xFE,0xFE,0xFE,0x00,0x00,0xFE,
  0xFF,0xFE,0xFE,0x00,0xFE,0xFF,0x00,0x00,0x00,0x00,0xFF,0x00,0x00,0x00,0x01,0xFF,
  0x00,0x00,0x00,0xFF,0x00,0x00,0x00,0xFF,0x00,0x00,0x00,0x00,0x00,0xFE,0x00,0xFF,
  0x00,0x00,0x00,0xFE,0xFF,0xFF,0xFE,0xFF,0xFE,0xFE,0xFE,0xFE,0xFE,0xFE,0xFE,0xFF,
  0xFE,0xFF,0xFE,0xFF,0xFE,0xFE,0xFE,0xFE,0xFF,0xFE,0xFE,0xFF,0xFE,0xFE,0xFE,0xFE,
  0xFE,0xFE,0xFE,0xFE,0xFE,0xFE,0xFE,0xFF,0x00,0x00,0x00,0xFF,0x00,0x00,0x00,0x01,
  0xFF,0x00,0x00,0x00,0x00,0x00,0x00,0x01,0x00,0x00,0x00,0x01,0x00,0x00,0x00,0x00,
  0x01,0x00,0xFF,0x00,0xFF,0x00,0xFF,0xFE,0x01,0xFE,0xFD,0xFD,0xFE,0xFF,0xFF,0xFE,
  0xFF,0xFF,0xFE,0xFE,0xFE,0xFE,0xFE,0xFE,0xFE,0xFF,0xFE,0xFE,0xFE,0xFE,0xFE,0xFD,
  0xFA,0xFA,0xFB,0xFB,0xFA,0xFB,0xFA,0xFA,0xFB,0xFB,0xFC,0xFA,0xFB,0xFB,0xFB,0xFB,
  0xFA,0xFE,0xFE,0xFF,0xFE,0xFE,0x01,0xFF,0x00,0x02,0x02,0x05,0x06,0x07,0x08,0x07,
  0x07,0x07,0x07,0x07,0x06,0x05,0x05,0x05,0x02,0x02,0x01,0x00,0x00,0x00,0xFE,0xFF,
  0xFA,0xFB,0xFA,0xFB,0xF9,0xFA,0xF4,0xF0,0xEE,0xEA,0xE9,0xE9,0xEB,0xEA,0xEF,0xF0,
  0xF0,0xF6,0xF6,0xFB,0xFF,0x00,0x02,0x02,0x05,0x07,0x0B,0x0C,0x0C,0x0D,0x10,0x0F,
  0x10,0x10,0x0F,0x0D,0x0D,0x0D,0x0C,0x0C,0x0A,0x0B,0x0A,0x08,0x07,0x07,0x06,0x05,
  0x01,0x01,0x02,0x02,0x00,0x00,0x01,0x00,0x04,0x0D,0x11,0x15,0x17,0x16,0x16,0x12,
  0x0D,0x08,0x05,0x01,0xFC,0xF5,0xF0,0xEA,0xE9,0xE6,0xE4,0xE0,0xDE,0xDF,0xDB,0xDB,
  0xDA,0xDB,0xDF,0xDF,0xDF,0xE1,0xE4,0xE4,0xE4,0xE0,0xDB,0xD8,0xD6,0xD6,0xD6,0xD9,
  0xDB,0xE0,0xE6,0xEB,0xF1,0xF6,0xFF,0x02,0x08,0x10,0x12,0x18,0x1C,0x22,0x25,0x26,
  0x2A,0x2C,0x30,0x30,0x30,0x2F,0x2C,0x2D,0x2D,0x2B,0x27,0x26,0x25,0x22,0x1F,0x21,
  0x27,0x30,0x36,0x3A,0x3A,0x3A,0x35,0x2D,0x25,0x1B,0x10,0x08,0xFE,0xF4,0xEA,0xE0,
  0xDA,0xD4,0xCA,0xC9,0xC4,0xC0,0xBF,0xBC,0xBB,0xBB,0xBB,0xBF,0xBF,0xC0,0xC5,0xC5,
  0xCB,0xCF,0xD4,0xD6,0xDB,0xE0,0xE4,0xE9,0xEE,0xF0,0xF6,0xF9,0xFB,0xFF,0x02,0x05,
  0x07,0x0B,0x0C,0x10,0x10,0x12,0x11,0x16,0x15,0x17,0x17,0x17,0x17,0x17,0x17,0x15,
  0x16,0x15,0x10,0x07,0x02,0xFB,0xF5,0xF4,0xF4,0xF1,0xF4,0xF3,0xF5,0xF9,0xFB,0xFF,
  0x00,0x01,0x07,0x0B,0x0C,0x10,0x12,0x11,0x16,0x17,0x17,0x1A,0x1A,0x1B,0x1B,0x1B,
  0x1A,0x1A,0x1A,0x17,0x17,0x17,0x15,0x11,0x11,0x0F,0x10,0x0C,0x0C,0x0C,0x0B,0x0B,
  0x0B,0x0C,0x1B,0x27,0x32,0x3C,0x40,0x40,0x37,0x30,0x27,0x1B,0x10,0x02,0xF5,0xEB,
  0xE0,0xD5,0xCB,0xC4,0xBC,0xB5,0xB4,0xAE,0xAC,0xAB,0xAB,0xAB,0xAB,0xAF,0xB1,0xB4,
  0xB6,0xBB,0xBE,0xBC,0xB9,0xB9,0xB9,0xBB,0xC1,0xC6,0xCA,0xD4,0xDB,0xE4,0xEB,0xF3,
  0xFE,0x06,0x0C,0x12,0x1B,0x20,0x27,0x2C,0x31,0x35,0x3A,0x3C,0x3F,0x42,0x49,0x5A,
  0x66,0x71,0x76,0x7A,0x76,0x71,0x6A,0x60,0x55,0x47,0x3A,0x2C,0x20,0x12,0x07,0xFB,
  0xF4,0xE9,0xE0,0xD8,0xD4,0xCF,0xC9,0xC6,0xC4,0xC1,0xC0,0xC1,0xC0,0xC0,0xC4,0xC6,
  0xC6,0xC9,0xCB,0xCE,0xD4,0xD5,0xD9,0xDE,0xE0,0xE5,0xE9,0xEF,0xF1,0xF4,0xF5,0xF9,
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
};
