harbaum/galagino/galagino/dkong_sample_walk0.h

const unsigned char dkong_sample_walk0[] = {
  0xFE,0xFE,0xFD,0xFF,0xFC,0xFE,0xFC,0xFE,0xFD,0xFD,0xFF,0xFD,0xFE,0xFD,0xFE,0xFC,
  0xFF,0xFD,0xFD,0xFF,0xFD,0xFE,0xFE,0xFD,0xFE,0xFD,0xFF,0xFC,0xFF,0xFF,0xFD,0xFF,
  0xFC,0xFF,0xFC,0xFF,0x01,0xFF,0xFF,0xFE,0x01,0xFE,0xFD,0xFF,0xFD,0xFE,0xFD,0xFC,
  0xFF,0xFD,0xFF,0xFD,0xFE,0xFC,0xFE,0x00,0xFF,0xFF,0xFE,0x00,0xFE,0x00,0x00,0xFE,
  0x00,0xFF,0xFF,0xFE,0xFE,0xFD,0xFD,0xFC,0xFD,0xFB,0xFB,0xF8,0xD7,0xA6,0x92,0xC6,
  0x07,0x22,0x2E,0x33,0x31,0x2D,0x24,0x1D,0x16,0x11,0x0F,0x08,0x02,0xEE,0xBB,0x91,
  0x83,0x90,0xA6,0xD3,0x23,0x55,0x64,0x68,0x60,0x57,0x4C,0x3D,0x31,0x27,0x1A,0x12,
  0x0B,0x03,0xFF,0xE8,0xB6,0x8C,0x82,0x86,0x96,0xC3,0x0B,0x3D,0x52,0x56,0x51,0x48,
  0x3D,0x32,0x28,0x1F,0x14,0x0E,0x03,0x00,0xFA,0xF2,0xED,0xD2,0xA3,0x84,0x83,0x8E,
  0xA2,0xD6,0x18,0x3D,0x49,0x4B,0x46,0x3E,0x32,0x28,0x1E,0x16,0x12,0x08,0x00,0xFE,
  0xFB,0xF4,0xEF,0xEA,0xCE,0xA5,0x8F,0x8B,0x96,0xAC,0xDA,0x1A,0x3C,0x44,0x48,0x42,
  0x38,0x2D,0x28,0x20,0x16,0x0E,0x0A,0x06,0xFD,0xFC,0xF9,0xF5,0xF1,0xEF,0xDD,0xB7,
  0x9B,0x94,0x9C,0xAD,0xCF,0x09,0x34,0x3E,0x42,0x41,0x38,0x2F,0x28,0x20,0x19,0x12,
  0x0D,0x04,0x01,0xFF,0xFD,0xF8,0xF5,0xF4,0xF1,0xEB,0xC9,0xA9,0xA2,0xA3,0xAE,0xC3,
  0xF7,0x25,0x39,0x40,0x3C,0x38,0x2F,0x29,0x23,0x1A,0x15,0x0E,0x0A,0x02,0x00,0xFE,
  0xFB,0xF6,0xF3,0xE2,0xC0,0xB1,0xA9,0xAF,0xBC,0xD8,0x07,0x27,0x36,0x39,0x38,0x31,
  0x29,0x21,0x1A,0x17,0x0F,0x09,0x07,0x00,0xFE,0xFB,0xF9,0xF0,0xD1,0xBC,0xB2,0xB2,
  0xBE,0xCE,0xF5,0x1B,0x2D,0x34,0x33,0x2F,0x27,0x22,0x1F,0x15,0x0F,0x09,0x04,0x00,
  0x00,0xFD,0xF8,0xE8,0xCB,0xBD,0xB8,0xBB,0xC8,0xDE,0x0A,0x22,0x2B,0x30,0x2C,0x2A,
  0x22,0x1D,0x16,0x0C,0x0A,0x04,0x01,0xFE,0xFC,0xF8,0xE6,0xCE,0xBC,0xBB,0xC2,0xCD,
  0xEA,0x0C,0x20,0x2A,0x2C,0x2A,0x24,0x1B,0x18,0x12,0x0B,0x08,0x02,0x00,0xFE,0xFB,
  0xEC,0xD7,0xC5,0xBE,0xC3,0xCC,0xE0,0x02,0x1A,0x25,0x29,0x27,0x22,0x1C,0x18,0x13,
  0x0C,0x0A,0x05,0x00,0xFE,0xFE,0xF0,0xD8,0xCA,0xC3,0xC8,0xD0,0xE1,0x02,0x18,0x22,
  0x23,0x22,0x1F,0x18,0x15,0x0E,0x0B,0x07,0x04,0x01,0xFE,0xF9,0xE7,0xD4,0xCB,0xC9,
  0xD1,0xD9,0xF3,0x0E,0x1B,0x22,0x21,0x1D,0x17,0x13,0x11,0x0A,0x08,0x03,0x01,0xFF,
  0xFD,0xF1,0xDB,0xD0,0xCB,0xD0,0xD8,0xEA,0x07,0x18,0x20,0x1F,0x1E,0x18,0x15,0x10,
  0x0B,0x09,0x05,0x01,0xFF,0xFC,0xF3,0xDE,0xD3,0xD3,0xD4,0xD9,0xEC,0x03,0x16,0x1D,
  0x1E,0x1B,0x16,0x13,0x0F,0x09,0x07,0x03,0x01,0xFE,0xFD,0xF2,0xE1,0xD6,0xD3,0xD5,
  0xDB,0xEC,0x03,0x14,0x1B,0x1B,0x18,0x16,0x13,0x0D,0x0A,0x07,0x03,0xFF,0x00,0xFD,
  0xF0,0xE0,0xD8,0xD6,0xD9,0xE3,0xF4,0x09,0x14,0x19,0x18,0x17,0x12,0x0E,0x0B,0x0A,
  0x05,0x01,0x02,0xFE,0xF9,0xEC,0xDC,0xD7,0xD9,0xDE,0xE8,0xFD,0x0C,0x13,0x18,0x16,
  0x14,0x10,0x0B,0x0A,0x06,0x03,0x02,0x00,0xFE,0xF8,0xE9,0xDC,0xDC,0xDD,0xE2,0xF0,
  0xFF,0x10,0x16,0x13,0x14,0x12,0x0C,0x0A,0x08,0x03,0x02,0x01,0xFE,0xFD,0xF3,0xE5,
  0xDF,0xDD,0xE0,0xE6,0xF7,0x06,0x0E,0x13,0x14,0x11,0x0E,0x0B,0x09,0x04,0x03,0x02,
  0x00,0xFE,0xF8,0xEC,0xE2,0xDF,0xE0,0xE4,0xEE,0x00,0x0B,0x10,0x12,0x13,0x0F,0x0C,
  0x0A,0x05,0x03,0x01,0x00,0xFE,0xFF,0xF4,0xE7,0xE1,0xE0,0xE3,0xE8,0xF5,0x03,0x0D,
  0x13,0x13,0x12,0x0D,0x0B,0x06,0x04,0x02,0x02,0x00,0x01,0xFB,0xEE,0xE6,0xE3,0xE4,
  0xE6,0xEF,0xFF,0x08,0x0F,0x10,0x0F,0x0C,0x09,0x08,0x04,0x03,0x01,0x02,0x00,0xFD,
  0xF4,0xE9,0xE6,0xE4,0xE9,0xEE,0xFA,0x05,0x0C,0x10,0x0E,0x0B,0x0B,0x09,0x05,0x03,
  0x01,0x00,0x01,0xFE,0xF8,0xF0,0xE8,0xE7,0xE8,0xEB,0xF4,0x00,0x0A,0x0D,0x0E,0x0E,
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
};
