harbaum/galagino/galagino/galaga_sample_boom.h

const unsigned char galaga_sample_boom[] = {
  0xFF,0xFF,0xFF,0xFF,0xFF,0xFF,0xFF,0xFF,0xFF,0xFF,0xFF,0xFF,0xFF,0xFF,0xFF,0x00,
  0xFF,0xFF,0xFF,0xFF,0xFF,0xFF,0xFF,0xFF,0xFF,0xFF,0xFF,0xFF,0xFF,0xFF,0xFF,0xFF,
  0xFF,0xFF,0xFF,0x00,0xFF,0xFF,0xFF,0xFF,0xFF,0xFF,0xFF,0xFF,0xFF,0xFF,0xFF,0xFF,
  0xFF,0xFF,0xFF,0xFF,0xFF,0xFF,0xFF,0xFF,0xFF,0xFF,0xFF,0xFF,0xFF,0xFF,0xFF,0xFF,
  0xFF,0xFF,0xFF,0xFF,0xFF,0xFF,0xFF,0xFF,0xFF,0xFF,0xFF,0xFF,0xFF,0xFF,0xFF,0xFF,
  0xFF,0xFF,0xFF,0xFF,0xFF,0xFF,0xFF,0xFF,0xFF,0xFF,0xFF,0xFF,0xFF,0xFF,0xFF,0xFF,
  0xFF,0xFF,0xFF,0xFF,0xFF,0xFF,0xFF,0xFF,0xFF,0xFF,0xFF,0xFF,0xFF,0xFF,0xFF,0xFF,
  0xFF,0xFF,0xFF,0xFF,0xFF,0xFF,0xFF,0xFF,0xFF,0xFF,0xFF,0xFF,0xFF,0xFF,0xFF,0xFF,
  0xFF,0xFF,0xFF,0xFF,0xFF,0xFF,0xFF,0xFF,0xFF,0xFF,0xFF,0x00,0xFF,0xFF,0xFF,0xFF,
  0xFF,0xFF,0xFF,0xFF,0xFF,0xFF,0xFF,0xFF,0xFF,0xFF,0xFF,0xFF,0xFF,0xFF,0xFF,0xFF,
  0xFF,0xFF,0xFF,0xFF,0xFF,0xFF,0xFF,0xFF,0xFF,0xFF,0xFF,0xFF,0x00,0xFF,0xFF,0xFF,
  0xFF,0x00,0xFF,0xFF,0xFF,0xFF,0xFF,0xFF,0xFF,0xFF,0xFF,0xFF,0xFF,0xFF,0xFF,0xFF,
  0xFF,0xFF,0xFF,0xFF,0xFF,0xFF,0x00,0xFF,0xFF,0xFF,0xFF,0xFF,0xFF,0xFF,0xFF,0xFF,
  0xFF,0xFF,0xFF,0xFF,0xFF,0xFF,0xFF,0xFF,0xFF,0xFF,0xFF,0xFF,0xFF,0xFF,0xFF,0xFF,
  0xFF,0x00,0xFF,0x00,0xFF,0xFF,0xFF,0xFF,0xFF,0xFF,0xFF,0xFF,0xFF,0xFE,0xFE,0xFF,
  0xFF,0xFF,0xFF,0xFF,0xFF,0xFF,0x00,0xFF,0xFF,0x00,0xFF,0xFF,0xFF,0xFF,0xFF,0x00,
  0xFF,0x00,0xFF,0xFF,0xFF,0xFF,0xFF,0xFF,0x00,0xFF,0x00,0x00,0xFF,0xFF,0xFF,0xFF,
  0xFF,0xFF,0x00,0xFF,0xFF,0xFF,0xFF,0xFF,0x00,0xFF,0xFF,0xFF,0xFF,0x00,0xFF,0xFF,
  0xFF,0xFF,0xFF,0xFF,0xFF,0x00,0xFF,0xFF,0xFF,0xFF,0xFF,0x00,0xFF,0x00,0xFF,0xFF,
  0xFF,0xFF,0xFF,0xFF,0xFF,0xF9,0xEE,0xE5,0xDB,0xD3,0xCA,0xC3,0xBC,0xB6,0xB1,0xAC,
  0xA8,0xA5,0xA4,0xA2,0xA2,0xA1,0xA2,0xA3,0xA6,0xA9,0xAC,0xAF,0xB5,0xC2,0xCD,0xD3,
  0xDA,0xDB,0xDB,0xDD,0xE1,0xE6,0xED,0xF4,0xFB,0x04,0x0B,0x12,0x19,0x1E,0x23,0x26,
  0x29,0x2A,0x2A,0x29,0x28,0x26,0x23,0x24,0x2E,0x3D,0x4C,0x55,0x55,0x52,0x4D,0x48,
  0x3F,0x3F,0x3D,0x34,0x2D,0x26,0x23,0x1F,0x1F,0x1C,0x14,0x0E,0x09,0x04,0x01,0x03,
  0x0E,0x1D,0x2B,0x30,0x2D,0x27,0x1F,0x14,0x08,0xFA,0xEC,0xDD,0xCF,0xC1,0xB8,0xB7,
  0xB1,0xAB,0xA8,0xA0,0x9A,0x98,0x99,0x9D,0xA3,0xAB,0xB4,0xBD,0xC6,0xD0,0xDF,0xF5,
  0x0F,0x23,0x2D,0x30,0x30,0x2E,0x29,0x24,0x25,0x21,0x19,0x13,0x0F,0x0D,0x0E,0x12,
  0x18,0x20,0x27,0x2F,0x36,0x3F,0x48,0x51,0x59,0x60,0x66,0x6A,0x6D,0x6D,0x6A,0x63,
  0x5C,0x4C,0x37,0x23,0x10,0xFC,0xEC,0xE4,0xE5,0xEA,0xED,0xE9,0xE0,0xD7,0xCD,0xC3,
  0xBA,0xAF,0xA6,0x9D,0x95,0x8F,0x8C,0x89,0x87,0x84,0x83,0x82,0x82,0x85,0x8A,0x91,
  0x98,0xA6,0xB7,0xC0,0xCB,0xD4,0xD7,0xDB,0xE1,0xE7,0xF0,0x00,0x18,0x33,0x4D,0x5E,
  0x65,0x6B,0x6D,0x6C,0x6A,0x6D,0x6B,0x5E,0x50,0x44,0x39,0x2D,0x21,0x17,0x13,0x19,
  0x27,0x37,0x44,0x48,0x47,0x45,0x40,0x38,0x33,0x32,0x27,0x1C,0x10,0x05,0xFC,0xF6,
  0xF1,0xEE,0xEE,0xEF,0xF2,0xF5,0xFA,0xFE,0x03,0x03,0xFC,0xF5,0xEE,0xE7,0xDF,0xD8,
  0xD0,0xC7,0xBF,0xB8,0xB1,0xAA,0xA4,0xA0,0x9B,0x99,0xA0,0xB0,0xC4,0xD6,0xE7,0xF6,
  0x03,0x0F,0x15,0x13,0x10,0x0B,0x08,0x03,0x06,0x0A,0x06,0x06,0x06,0x09,0x0D,0x15,
  0x19,0x18,0x18,0x19,0x1A,0x1B,0x1C,0x1D,0x1C,0x1A,0x17,0x12,0x0E,0x08,0x02,0xFB,
  0xF4,0xF4,0xFC,0x07,0x13,0x16,0x13,0x0E,0x07,0x01,0xFA,0xF3,0xEC,0xE6,0xDF,0xD9,
  0xD4,0xD0,0xCE,0xCB,0xCA,0xCB,0xCB,0xCE,0xCF,0xD2,0xD5,0xDD,0xEA,0xEF,0xF4,0xFA,
  0x01,0x0A,0x12,0x1D,0x20,0x1F,0x20,0x21,0x21,0x22,0x21,0x21,0x1F,0x1E,0x1A,0x17,
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
};
