harbaum/galagino/galagino/dkong_sample_walk1.h

const unsigned char dkong_sample_walk1[] = {
  0xFF,0xFC,0xFE,0xFD,0xFF,0xFD,0xFF,0xFD,0xFE,0x00,0xFF,0x00,0xFF,0xFF,0xFF,0xFF,
  0xFD,0xFF,0xFD,0xFD,0xFE,0xFD,0xFE,0xFC,0xFA,0xE8,0xB5,0x8C,0x85,0x8F,0xA7,0xD7,
  0x21,0x57,0x6B,0x6C,0x64,0x5C,0x50,0x41,0x36,0x2D,0x24,0x19,0x10,0x08,0xF6,0xC8,
  0x98,0x86,0x8B,0x9A,0xC1,0x08,0x43,0x58,0x5A,0x57,0x4D,0x43,0x36,0x2A,0x1F,0x17,
  0x0D,0x04,0x00,0xF8,0xF1,0xDB,0xAA,0x89,0x81,0x8B,0x9F,0xCD,0x11,0x3B,0x4B,0x4E,
  0x48,0x3F,0x34,0x2C,0x23,0x18,0x10,0x06,0xFF,0xFE,0xF8,0xF4,0xEE,0xD9,0xB1,0x90,
  0x85,0x8F,0xA0,0xC8,0x0A,0x36,0x45,0x49,0x44,0x3B,0x30,0x28,0x1F,0x18,0x12,0x0B,
  0x01,0x00,0xFC,0xF6,0xF3,0xEF,0xE7,0xC5,0xA0,0x92,0x93,0xA1,0xB6,0xF0,0x26,0x3A,
  0x44,0x41,0x3A,0x34,0x2A,0x23,0x1D,0x17,0x0F,0x08,0x01,0xFF,0xFD,0xFA,0xF5,0xF3,
  0xF0,0xE0,0xBC,0x9F,0x9B,0xA2,0xAF,0xD2,0x0A,0x2E,0x3F,0x3F,0x3B,0x36,0x2B,0x27,
  0x20,0x17,0x14,0x0C,0x05,0x01,0xFF,0xFD,0xF9,0xF5,0xF7,0xF4,0xEE,0xDA,0xBA,0xA7,
  0xA4,0xAD,0xBD,0xE3,0x14,0x2F,0x39,0x3C,0x37,0x30,0x27,0x20,0x1B,0x17,0x0E,0x0C,
  0x05,0x02,0x00,0xFD,0xFC,0xF8,0xF4,0xF5,0xF3,0xEB,0xD4,0xB9,0xAE,0xB0,0xB8,0xCD,
  0xF9,0x1E,0x2F,0x36,0x36,0x2E,0x2A,0x26,0x1D,0x16,0x13,0x0E,0x0A,0x03,0x00,0x00,
  0xFF,0xFD,0xFC,0xF7,0xF5,0xF5,0xF3,0xE5,0xCB,0xBA,0xB5,0xBA,0xC7,0xDE,0x05,0x26,
  0x2F,0x31,0x31,0x2B,0x23,0x1E,0x1A,0x14,0x0D,0x0C,0x08,0x03,0x00,0xFE,0xFE,0xFB,
  0xFD,0xFB,0xF6,0xF4,0xF5,0xEE,0xDA,0xC5,0xBD,0xBB,0xC7,0xD7,0xF5,0x17,0x27,0x2B,
  0x2A,0x29,0x24,0x1C,0x1A,0x15,0x0E,0x0B,0x08,0x02,0x02,0xFF,0xFE,0xFE,0xFC,0xFB,
  0xFA,0xF6,0xF5,0xF4,0xF0,0xDF,0xCA,0xC2,0xC3,0xCA,0xD8,0xF3,0x13,0x24,0x2A,0x29,
  0x22,0x21,0x1B,0x15,0x12,0x0D,0x0B,0x06,0x01,0x00,0xFE,0xFE,0xFC,0xFD,0xFA,0xFC,
  0xFC,0xF7,0xF5,0xF4,0xEE,0xDB,0xD0,0xCA,0xCD,0xD6,0xE4,0x02,0x15,0x22,0x27,0x23,
  0x20,0x19,0x16,0x15,0x0E,0x0B,0x07,0x04,0x01,0x00,0xFF,0xFD,0xFC,0xFB,0xFB,0xF9,
  0xF7,0xF2,0xE4,0xD5,0xCF,0xD0,0xD9,0xE0,0xF6,0x10,0x1A,0x20,0x1E,0x1D,0x18,0x15,
  0x10,0x0D,0x0A,0x05,0x03,0x02,0x00,0xFF,0xFD,0xFB,0xFB,0xF9,0xF3,0xE5,0xD9,0xD5,
  0xD5,0xDA,0xE5,0xF9,0x0E,0x16,0x1B,0x1C,0x16,0x13,0x11,0x0F,0x0B,0x08,0x05,0x04,
  0x01,0x00,0xFF,0xFD,0xFC,0xF8,0xEF,0xDE,0xD7,0xD8,0xDD,0xE5,0xF6,0x09,0x13,0x18,
  0x19,0x18,0x14,0x10,0x0D,0x09,0x09,0x01,0x00,0x00,0xFE,0xFF,0xFB,0xFB,0xF3,0xE6,
  0xDC,0xDD,0xDD,0xE1,0xF1,0x03,0x10,0x15,0x18,0x16,0x13,0x0E,0x0E,0x0A,0x05,0x01,
  0x02,0x00,0xFF,0xFD,0xFB,0xF8,0xEC,0xE1,0xDD,0xDF,0xE0,0xEA,0xFD,0x0B,0x12,0x15,
  0x13,0x14,0x0F,0x09,0x09,0x06,0x03,0x01,0xFF,0xFF,0xFF,0xFD,0xF5,0xEB,0xE4,0xDF,
  0xE2,0xE6,0xEE,0xFD,0x07,0x10,0x13,0x11,0x0E,0x0B,0x09,0x08,0x04,0x03,0x02,0x00,
  0xFE,0xFD,0xFE,0xF4,0xEA,0xE3,0xE4,0xE7,0xEA,0xF8,0x05,0x0D,0x13,0x12,0x10,0x0C,
  0x0B,0x09,0x04,0x03,0x01,0xFF,0xFE,0xFF,0xFC,0xF3,0xEC,0xE6,0xE3,0xE6,0xEA,0xF4,
  0x02,0x09,0x0E,0x10,0x0E,0x0A,0x0A,0x08,0x03,0x03,0x01,0x01,0xFF,0xFE,0xFC,0xF4,
  0xEB,0xE6,0xE6,0xEA,0xEE,0xF8,0x05,0x0A,0x0C,0x0E,0x0B,0x0A,0x0A,0x03,0x03,0x02,
  0x01,0x01,0xFE,0xFC,0xFA,0xF1,0xEA,0xE6,0xE8,0xEC,0xF3,0xFF,0x09,0x0B,0x0B,0x0D,
  0x0B,0x09,0x07,0x03,0x03,0x03,0x00,0xFE,0x00,0xFD,0xF5,0xEE,0xF7,0x0F,0x22,0x23,
  0x17,0x04,0xF7,0xEE,0xEB,0xED,0xED,0xEF,0xF4,0xF5,0xF3,0xF6,0xFB,0x03,0x16,0x20,
  0x21,0x1E,0x16,0x09,0xF2,0xE2,0xDA,0xD5,0xD8,0xDE,0xE3,0xE7,0xE9,0xEF,0xF5,0xFE,
  0x11,0x20,0x24,0x21,0x1C,0x10,0xF9,0xE6,0xDF,0xDC,0xDF,0xE2,0xE8,0xEB,0xF2,0xF5,
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
};
