harbaum/galagino/galagino/dkong_sample_walk2.h

const unsigned char dkong_sample_walk2[] = {
  0xFE,0xFF,0x01,0xFE,0xFE,0xFD,0xFE,0xFD,0xFF,0xFC,0xFD,0xFF,0xFC,0xFE,0xFD,0xFF,
  0xFE,0xFF,0xFF,0x00,0xFE,0xFE,0xFD,0xFB,0xFD,0xFB,0xFC,0xFA,0xF3,0xD7,0xA6,0x84,
  0x81,0x94,0xAF,0xEB,0x3A,0x5F,0x6A,0x6C,0x62,0x56,0x4A,0x39,0x2F,0x0F,0xD6,0xA9,
  0x97,0x9E,0xAF,0xE1,0x2C,0x55,0x64,0x61,0x57,0x4B,0x3B,0x2F,0x25,0x14,0xE9,0xB4,
  0x92,0x8C,0x95,0xB1,0xF5,0x32,0x4D,0x53,0x4E,0x45,0x38,0x2F,0x1E,0x13,0x06,0xDB,
  0xAB,0x8E,0x8B,0x97,0xB2,0xF2,0x2D,0x45,0x4C,0x46,0x3C,0x32,0x26,0x1F,0x12,0x03,
  0xE5,0xB3,0x95,0x8C,0x92,0xA6,0xDF,0x20,0x3B,0x45,0x44,0x38,0x32,0x27,0x1F,0x13,
  0x0B,0xFE,0xD3,0xA8,0x94,0x93,0x9F,0xBE,0xFB,0x2C,0x40,0x44,0x3F,0x35,0x2B,0x20,
  0x19,0x10,0x06,0xF6,0xCE,0xA8,0x98,0x9B,0xA8,0xC9,0x08,0x2F,0x3D,0x41,0x3C,0x34,
  0x2A,0x1F,0x18,0x0E,0x06,0xFB,0xD7,0xAE,0xA0,0xA0,0xAB,0xC8,0x00,0x2B,0x3B,0x3F,
  0x3C,0x33,0x2C,0x21,0x1A,0x10,0x06,0x00,0xE5,0xBE,0xA8,0xA5,0xAD,0xBF,0xEB,0x1C,
  0x34,0x3A,0x38,0x33,0x2A,0x22,0x1C,0x13,0x0D,0x07,0xF6,0xD2,0xB6,0xA9,0xAC,0xB6,
  0xD3,0x04,0x26,0x35,0x38,0x35,0x2F,0x25,0x1E,0x16,0x10,0x08,0x00,0xEC,0xCB,0xB5,
  0xAD,0xB4,0xC1,0xE7,0x14,0x2B,0x37,0x36,0x30,0x28,0x20,0x1A,0x13,0x0C,0x05,0x00,
  0xE7,0xC7,0xB6,0xB3,0xB9,0xC7,0xED,0x19,0x2E,0x33,0x31,0x2C,0x27,0x1F,0x18,0x14,
  0x0C,0x03,0xFF,0xE8,0xCA,0xB9,0xB4,0xBB,0xCB,0xEC,0x15,0x2A,0x2D,0x2B,0x2A,0x22,
  0x1A,0x14,0x0C,0x0A,0x05,0x00,0xED,0xD0,0xBE,0xB9,0xC0,0xCB,0xE8,0x0E,0x23,0x2A,
  0x2B,0x2A,0x24,0x1B,0x15,0x0F,0x0C,0x06,0x01,0xF6,0xDB,0xC7,0xBE,0xC0,0xCB,0xDC,
  0xFF,0x1B,0x28,0x2B,0x2A,0x24,0x1C,0x17,0x0E,0x0B,0x06,0x02,0xFB,0xE5,0xD2,0xC4,
  0xC0,0xC9,0xD6,0xF5,0x12,0x22,0x2A,0x25,0x22,0x1C,0x17,0x12,0x0B,0x09,0x02,0x00,
  0xF5,0xDB,0xCC,0xC8,0xCA,0xD0,0xE6,0x08,0x1B,0x26,0x27,0x21,0x1E,0x17,0x13,0x0D,
  0x0A,0x04,0x02,0xFF,0xEB,0xD3,0xCB,0xCA,0xCE,0xD9,0xF3,0x0F,0x1C,0x21,0x22,0x1D,
  0x17,0x13,0x0D,0x0B,0x06,0x01,0x00,0xFA,0xE6,0xD3,0xCD,0xCE,0xD4,0xE0,0xFF,0x13,
  0x1D,0x22,0x1D,0x19,0x16,0x12,0x0C,0x0A,0x08,0xFF,0x00,0xF8,0xE3,0xD3,0xCE,0xD2,
  0xD6,0xE8,0x05,0x14,0x1F,0x1F,0x1A,0x17,0x12,0x0E,0x0C,0x07,0x01,0x00,0xFF,0xF3,
  0xE2,0xD3,0xD1,0xD4,0xD9,0xED,0x0A,0x14,0x1B,0x20,0x1B,0x17,0x12,0x0F,0x0B,0x05,
  0x04,0x01,0xFF,0xF2,0xE1,0xD7,0xD3,0xD7,0xE0,0xF1,0x07,0x15,0x1A,0x18,0x19,0x14,
  0x10,0x0C,0x0A,0x07,0x01,0xFF,0xFC,0xF0,0xE0,0xD6,0xD6,0xD8,0xE0,0xF3,0x08,0x13,
  0x18,0x19,0x14,0x13,0x0E,0x0C,0x08,0x03,0x02,0xFE,0xFD,0xF2,0xE2,0xDB,0xD8,0xDC,
  0xE3,0xF5,0x0A,0x11,0x17,0x18,0x15,0x12,0x0C,0x0A,0x08,0x04,0x02,0x01,0xFC,0xF5,
  0xE5,0xDC,0xDA,0xDC,0xE5,0xF3,0x08,0x12,0x16,0x16,0x14,0x12,0x0D,0x0A,0x05,0x02,
  0x02,0xFE,0xFF,0xF5,0xE8,0xDF,0xDD,0xDE,0xE4,0xF3,0x03,0x11,0x14,0x14,0x13,0x11,
  0x0B,0x09,0x06,0x02,0x02,0x00,0x00,0xF6,0xE8,0xE1,0xDF,0xE0,0xE7,0xF1,0x01,0x0E,
  0x12,0x15,0x13,0x12,0x0D,0x09,0x08,0x03,0x03,0x00,0xFE,0xF9,0xEA,0xE3,0xDE,0xE1,
  0xE6,0xF0,0xFE,0x0B,0x12,0x12,0x11,0x0D,0x0E,0x0A,0x03,0x01,0x01,0x00,0x00,0xFD,
  0xF3,0xE8,0xE3,0xE1,0xE5,0xEB,0xF8,0x05,0x0F,0x13,0x12,0x0F,0x0B,0x0C,0x09,0x05,
  0x04,0x02,0x00,0x01,0xFE,0xFD,0xF6,0xEB,0xE5,0xE1,0xE3,0xE8,0xF3,0x00,0x0B,0x10,
  0x0F,0x10,0x0D,0x08,0x0A,0x07,0x03,0x02,0x01,0x02,0x00,0xFF,0x00,0x08,0x19,0x22,
  0x21,0x22,0x1A,0x09,0xF5,0xE3,0xD7,0xD2,0xD4,0xD6,0xDD,0xDF,0xE3,0xE6,0xEB,0xF1,
  0xF3,0xF9,0xFC,0x03,0x16,0x23,0x28,0x25,0x21,0x13,0xFC,0xEA,0xDF,0xD7,0xDB,0xDE,
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
};
